theBrutzler/U-Bootloader/Software/dorRied/uboot/block.h

const unsigned char block[14][378] PROGMEM = {
  // BLOCK1
0x00, 0x01, 0xFF, 0xFF, 0xFF, 0x80, 0x00, 0x00, 0x03, 0xFF, 0xFF, 0xFF, 0xC0, 0x00, 0x00, 0x07,
0xFF, 0xFF, 0xFF, 0xE0, 0x00, 0x00, 0x0F, 0x00, 0x00, 0x00, 0xF0, 0x00, 0x00, 0x0E, 0x00, 0x00,
0x00, 0x70, 0x00, 0x00, 0x1E, 0x00, 0x00, 0x00, 0x78, 0x00, 0x00, 0x1C, 0x00, 0x00, 0x00, 0x38,
0x00, 0x00, 0x3C, 0x00, 0x00, 0x00, 0x3C, 0x00, 0x00, 0x78, 0x00, 0x00, 0x00, 0x1E, 0x00, 0x00,
0x70, 0x00, 0x00, 0x00, 0x0E, 0x00, 0x00, 0xF0, 0x00, 0x00, 0x00, 0x0F, 0x00, 0x01, 0xFF, 0xFF,
0xFF, 0xFF, 0xFF, 0x80, 0x01, 0xFF, 0xFF, 0xFF, 0xFF, 0xFF, 0x80, 0x01, 0xFF, 0xFF, 0xFF, 0xFF,
0xFF, 0x80, 0x01, 0xC0, 0x00, 0x00, 0x00, 0x03, 0x80, 0x01, 0xC0, 0x00, 0x00, 0x00, 0x03, 0x80,
0x01, 0xC0, 0x00, 0x00, 0xE0, 0x03, 0x80, 0x01, 0xC3, 0x80, 0x01, 0xF0, 0x03, 0x80, 0x01, 0xC3,
0x80, 0x03, 0xF8, 0x03, 0x80, 0x01, 0xC3, 0x80, 0x07, 0xFC, 0x03, 0x80, 0x01, 0xC3, 0x80, 0x0F,
0xFE, 0x03, 0x80, 0x01, 0xC3, 0x80, 0x0F, 0xFE, 0x03, 0x80, 0x01, 0xC3, 0x80, 0x0E, 0xEE, 0x03,
0x80, 0x01, 0xC3, 0x80, 0x00, 0xE0, 0x03, 0x80, 0x01, 0xC3, 0x80, 0x00, 0xE0, 0x03, 0x80, 0x01,
0xC3, 0x80, 0x00, 0xE0, 0x03, 0x80, 0x01, 0xC3, 0x80, 0x00, 0xE1, 0xC3, 0x80, 0x01, 0xC3, 0x80,
0x00, 0xE3, 0xC3, 0x80, 0x01, 0xC3, 0x87, 0x00, 0xE7, 0xC3, 0x80, 0x01, 0xC3, 0x8F, 0x00, 0xEF,
0xC3, 0x80, 0x01, 0xC3, 0x9F, 0x00, 0xFF, 0xC3, 0x80, 0x01, 0xC3, 0xBF, 0x00, 0xFF, 0xC3, 0x80,
0x01, 0xC3, 0xFF, 0x00, 0xFD, 0xC3, 0x80, 0x01, 0xC3, 0xFF, 0x00, 0xF9, 0xC3, 0x80, 0x01, 0xC3,
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
0x00, 0xFE, 0x00, 0x00, 0x00, 0x00, 0x1C, 0x00, 0x7E, 0x00, 0x00, 0x00, 0x00, 0x1C, 0x00, 0x3F,
0xFF, 0xFF, 0xFF, 0xFF, 0xFC, 0x00, 0x1F, 0xFF, 0xFF, 0xFF, 0xFF, 0xFC, 0x00, 0x0F, 0xFF, 0xFF,
0xFF, 0xFF, 0xFC, 0x00, 0x00, 0x00, 0x00, 0x00, 0x00, 0x00, 
};
