theBrutzler/U-Bootloader/Software/Penoids/penoid.h

#pragma once
#define SIZE 16

const unsigned char penoid [] PROGMEM = {
	0x01, 0x80, 0x03, 0xc0, 0x04, 0x20, 0x04, 0x20, 0x07, 0xe0, 0x04, 0x20, 0x04, 0x20, 0x04, 0x20, 
	0x0c, 0x30, 0x34, 0x2c, 0x44, 0x22, 0x44, 0x22, 0x40, 0x02, 0x40, 0x02, 0x30, 0x0c, 0x0c, 0x30
};
